SuperHouse/AQS/Images/AQSBCASE-v1_0-black-oblique.jpg

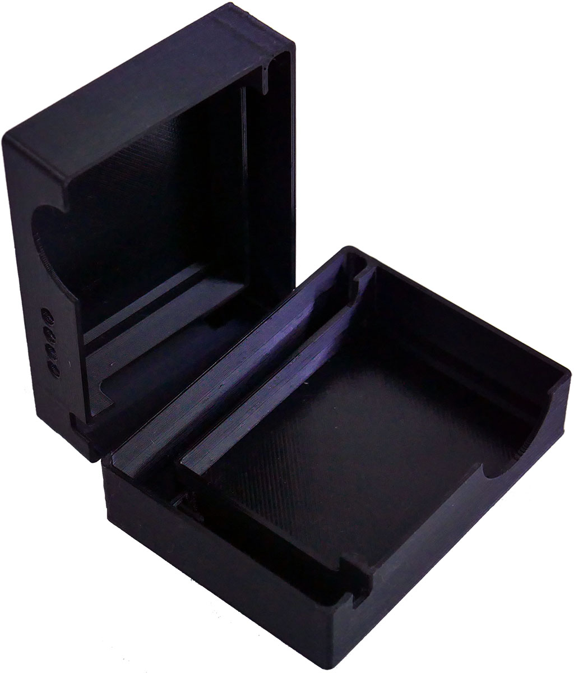
Images/AQSBCASE-v1_0-black-oblique.jpg
