SuperHouse/AQS/Images/AQSBCASE-v1_0-black-top.jpg

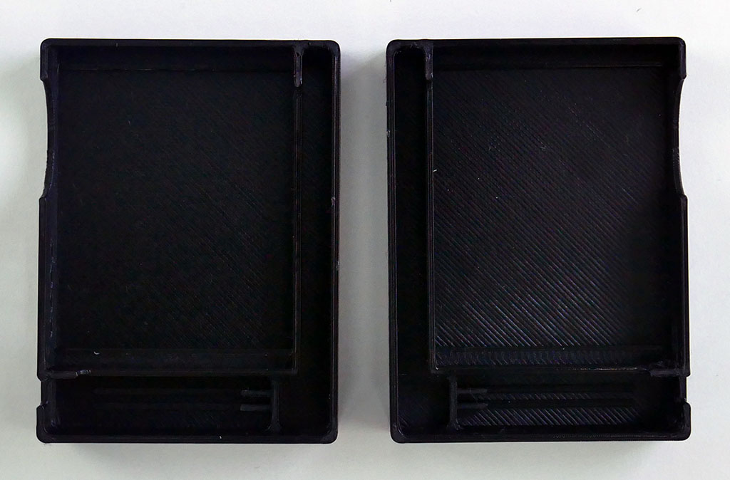
Images/AQSBCASE-v1_0-black-top.jpg
