SuperHouse/AQS/Images/AQSBCASE-v1_0-blue-top.jpg

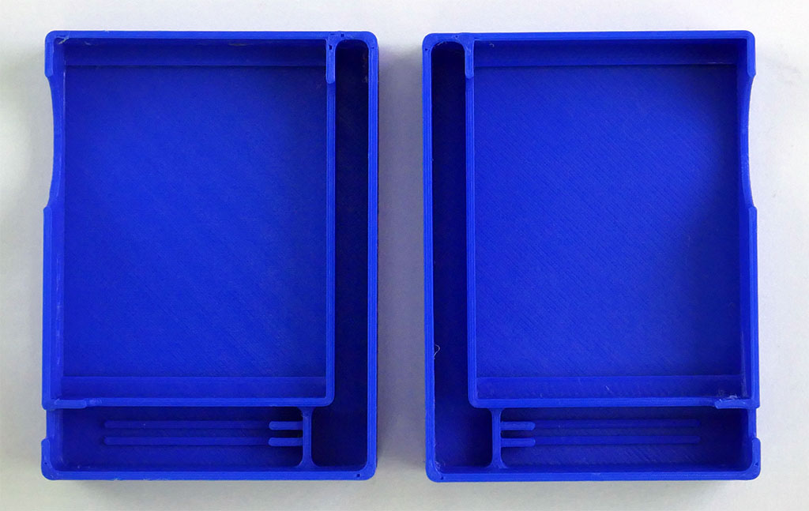
Images/AQSBCASE-v1_0-blue-top.jpg
