SuperHouse/AQS/Images/AQSBCASE-v1_0-green-oblique.jpg

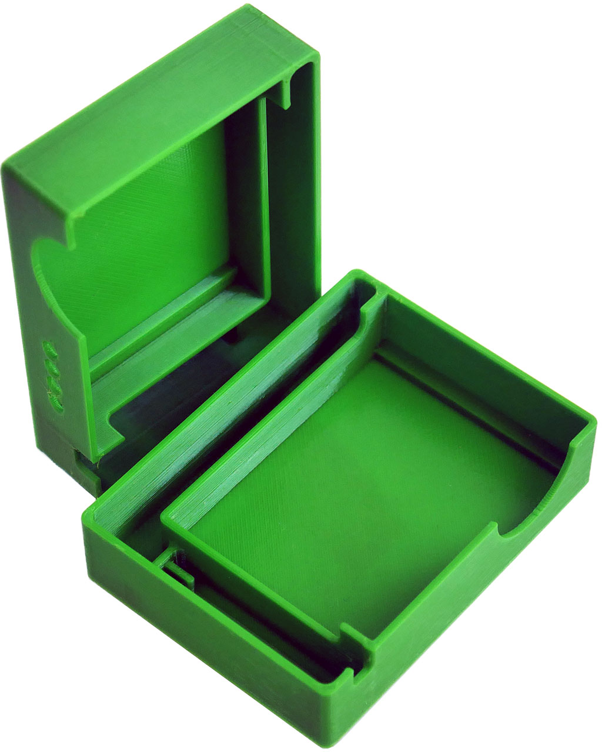
Images/AQSBCASE-v1_0-green-oblique.jpg
