SuperHouse/AQS/Images/AQSBCASE-v1_0-red-oblique.jpg

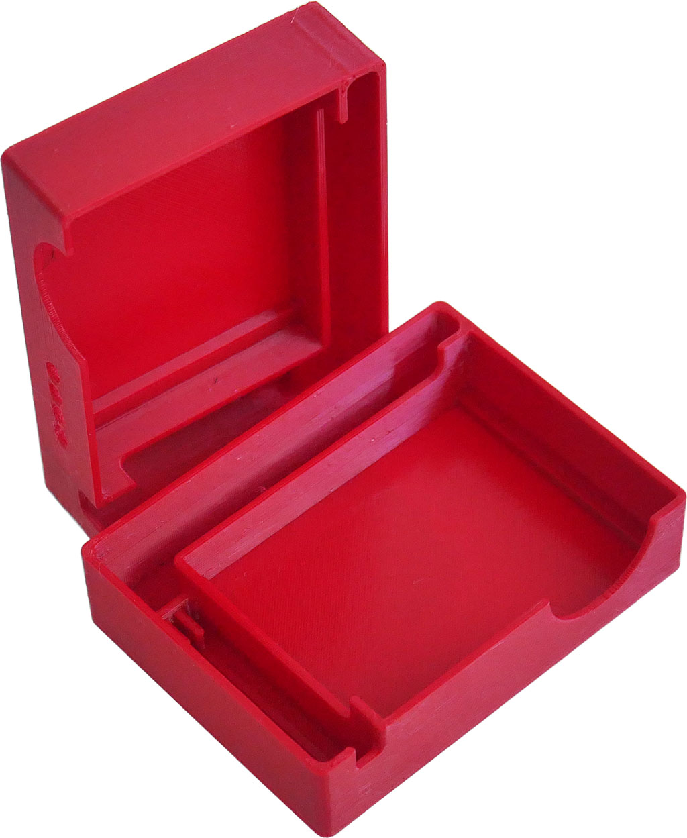
Images/AQSBCASE-v1_0-red-oblique.jpg
