SuperHouse/AQS/Images/AQSBCASE-v1_0-white-oblique.jpg

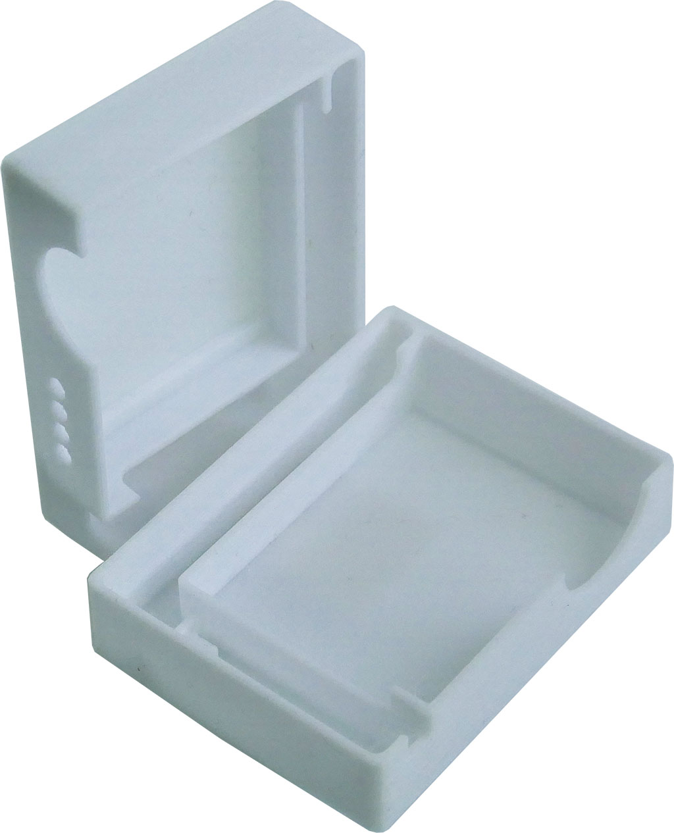
Images/AQSBCASE-v1_0-white-oblique.jpg
