SuperHouse/AQS/Images/AQSBCASE-v1_0-white-top.jpg

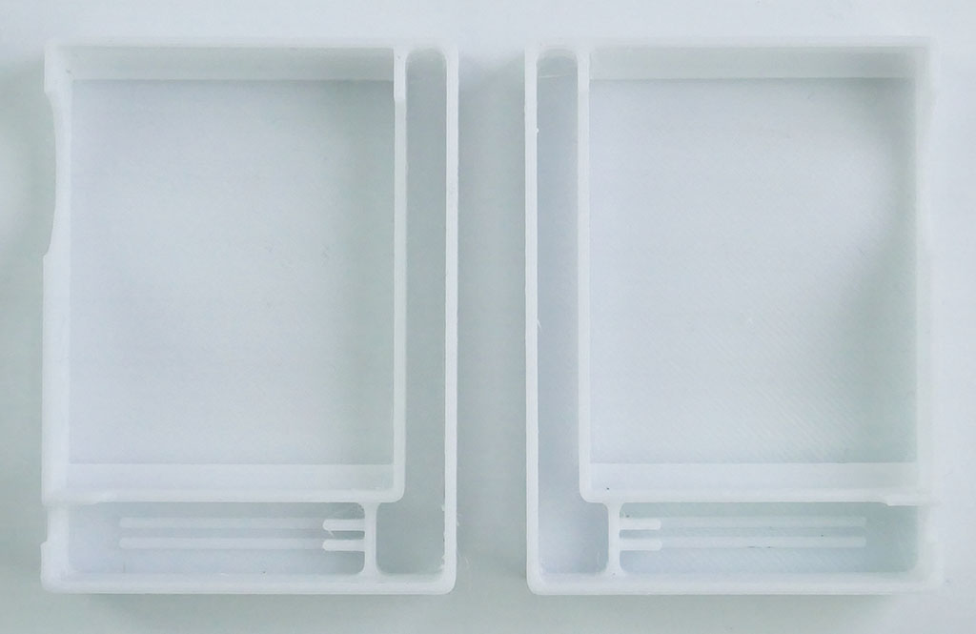
Images/AQSBCASE-v1_0-white-top.jpg
