SuperHouse/AQS/Images/AQSBCASE-v1_0-yellow-top.jpg

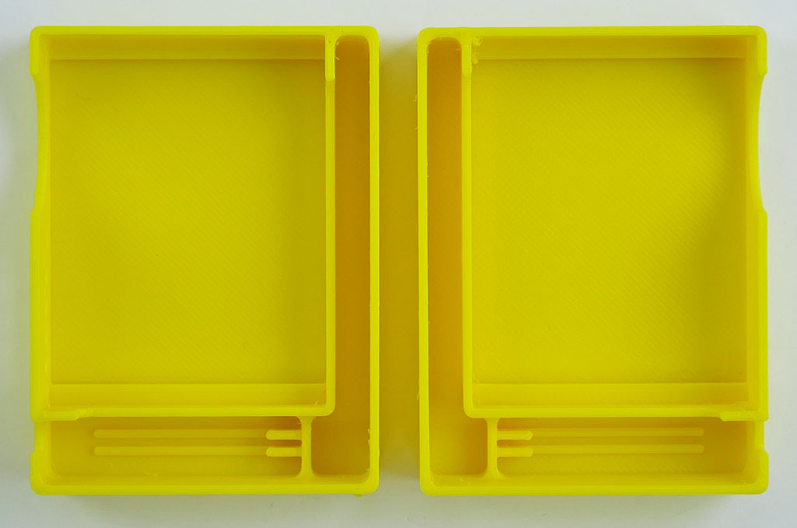
Images/AQSBCASE-v1_0-yellow-top.jpg
