SuperHouse/AQS/Images/AQSDCASE-v1_0-black-oblique.jpg

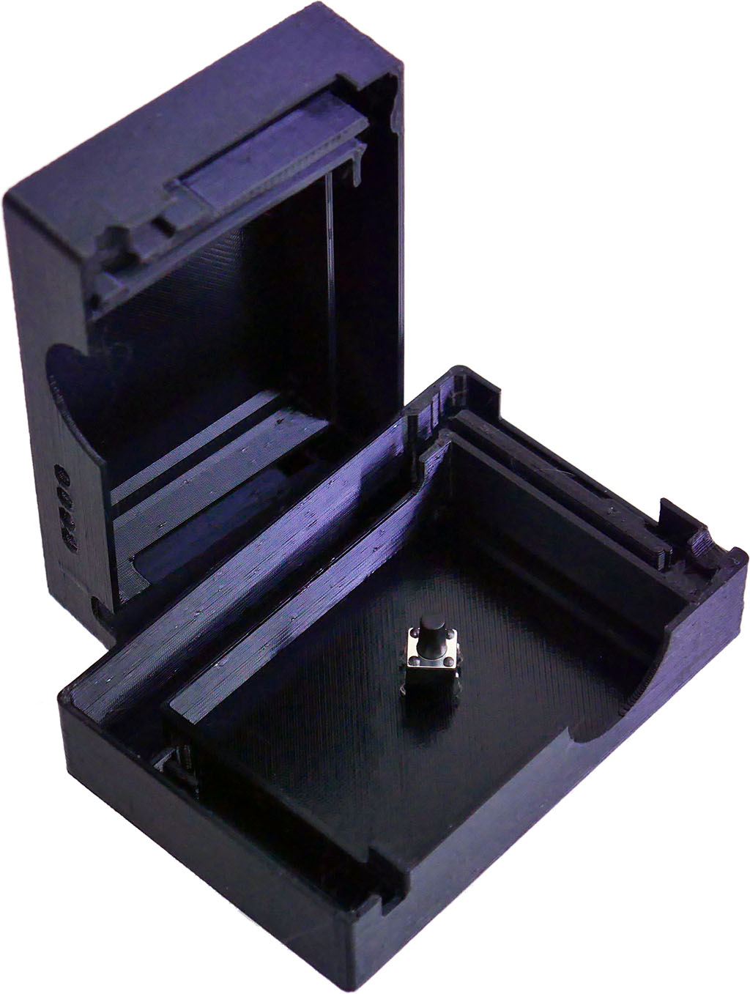
Images/AQSDCASE-v1_0-black-oblique.jpg
