SuperHouse/AQS/Images/AQSDCASE-v1_0-black-top.jpg

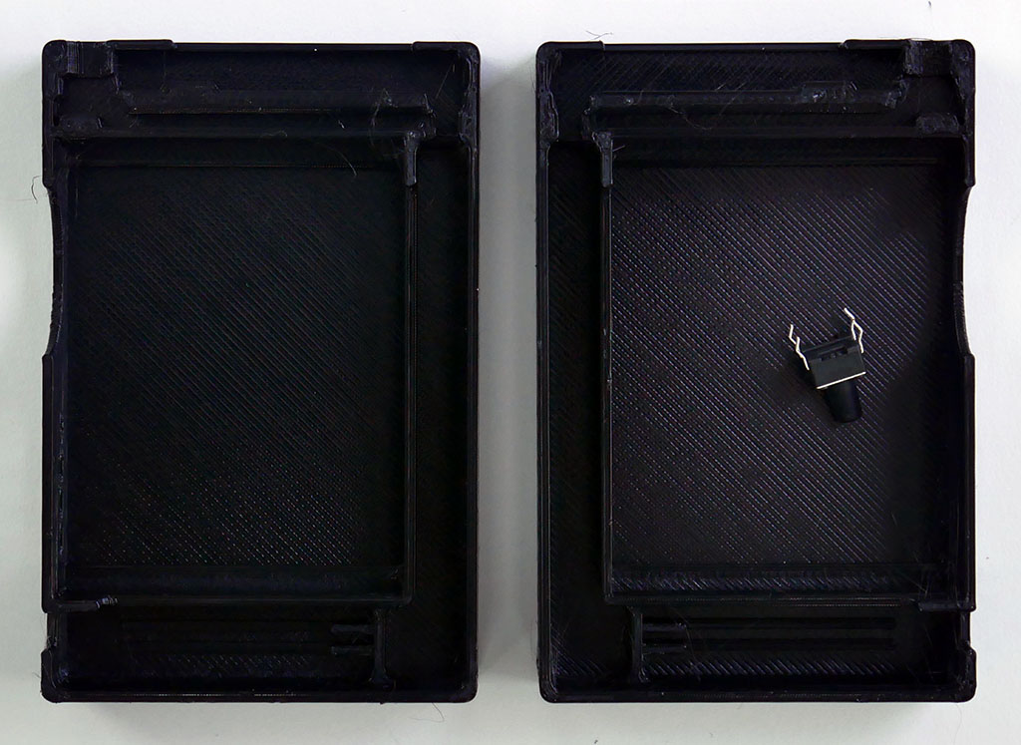
Images/AQSDCASE-v1_0-black-top.jpg
