SuperHouse/AQS/Images/AQSDCASE-v1_0-blue-oblique.jpg

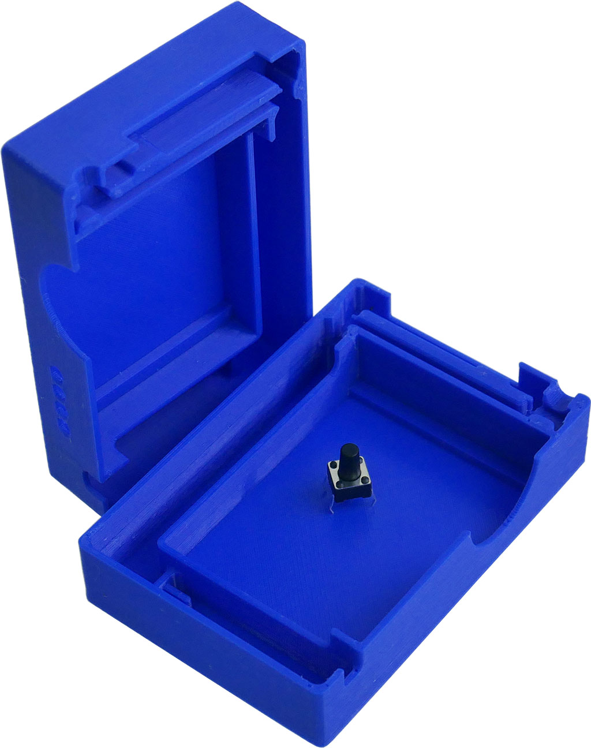
Images/AQSDCASE-v1_0-blue-oblique.jpg
