SuperHouse/AQS/Images/AQSDCASE-v1_0-blue-top.jpg

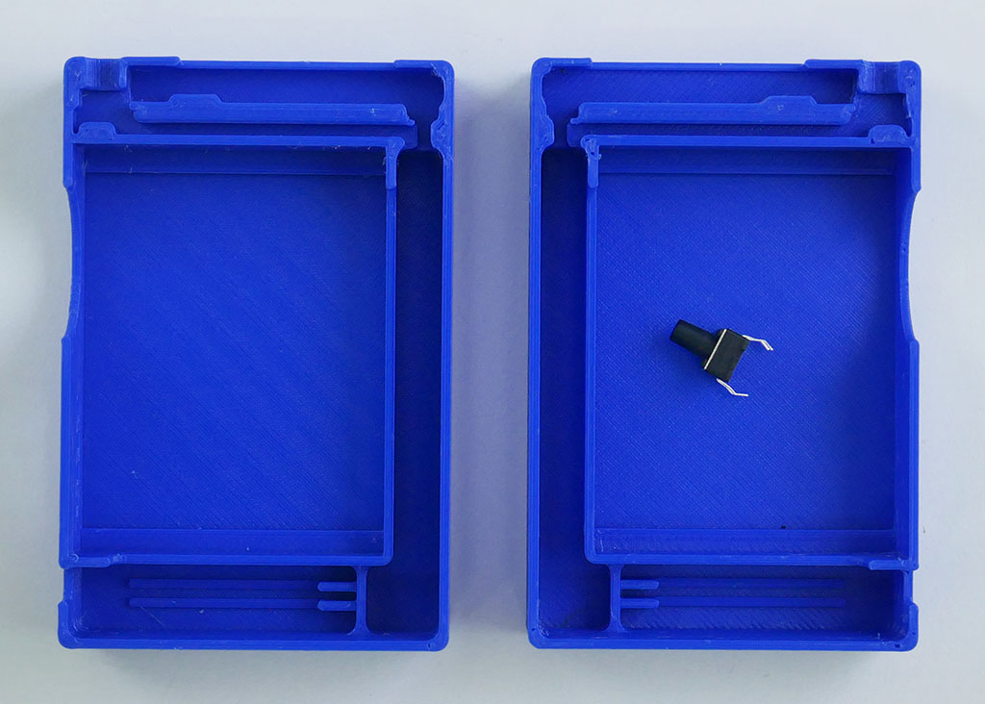
Images/AQSDCASE-v1_0-blue-top.jpg
