SuperHouse/AQS/Images/AQSDCASE-v1_0-translucent-oblique.jpg

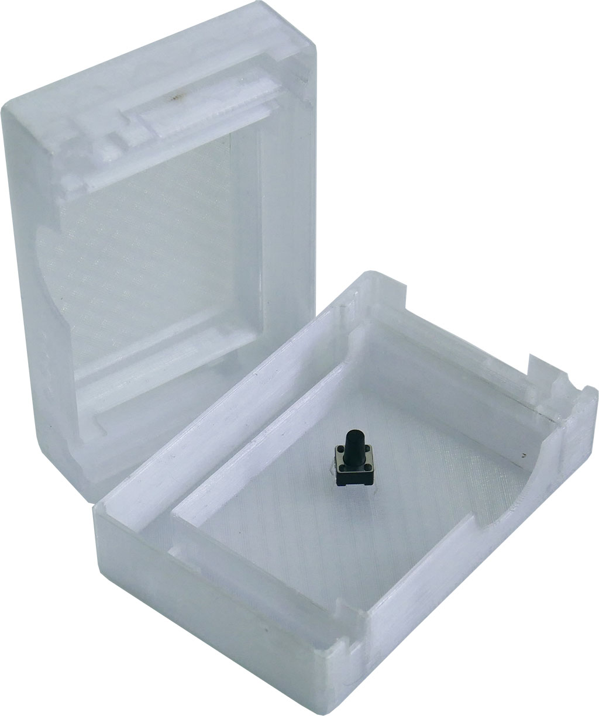
Images/AQSDCASE-v1_0-translucent-oblique.jpg
