SuperHouse/AQS/Images/AQSDCASE-v1_0-translucent-top.jpg

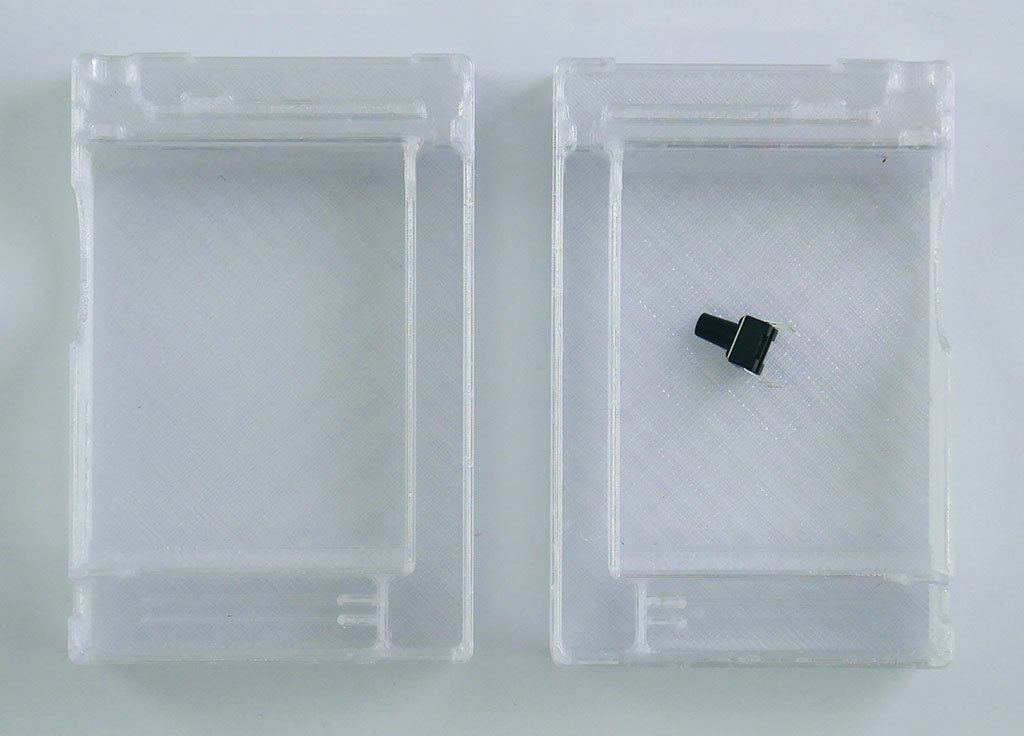
Images/AQSDCASE-v1_0-translucent-top.jpg
