SuperHouse/AQS/Images/AQSDCASE-v1_0-white-oblique.jpg

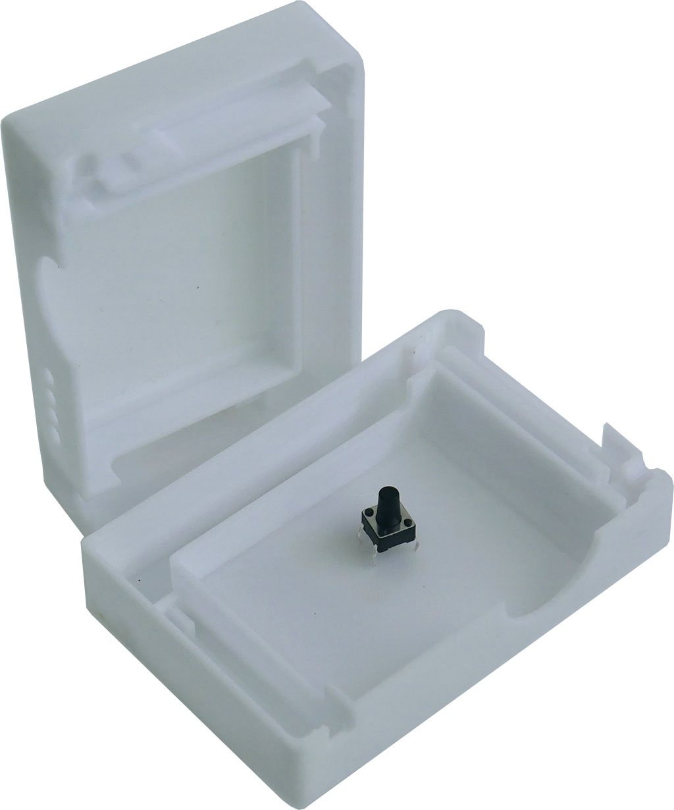
Images/AQSDCASE-v1_0-white-oblique.jpg
