SuperHouse/AQS/Images/AQSDCASE-v1_0-yellow-oblique.jpg

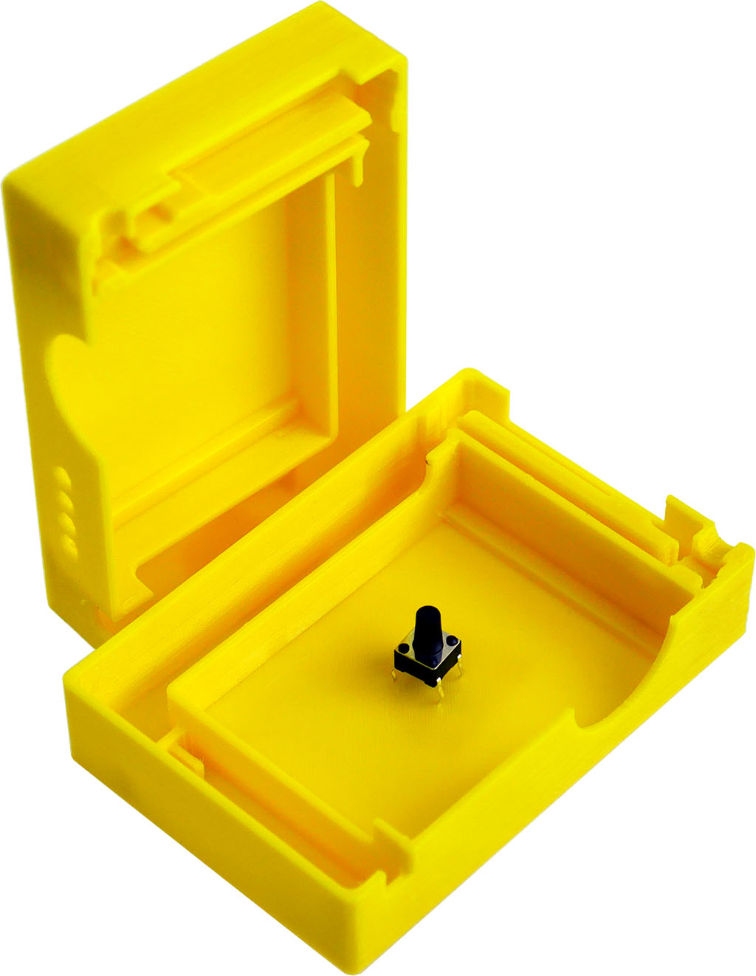
Images/AQSDCASE-v1_0-yellow-oblique.jpg
