SuperHouse/AQS/Images/AQSDCASE-v1_0-yellow-top.jpg

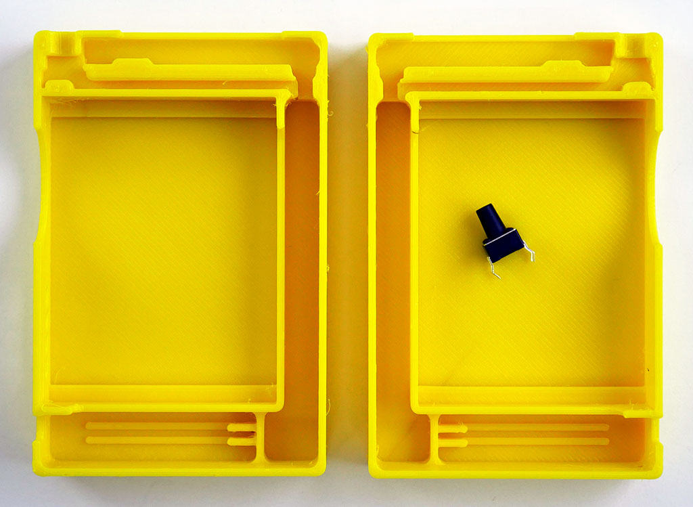
Images/AQSDCASE-v1_0-yellow-top.jpg
