SuperHouse/AQS/Images/P1030344.png

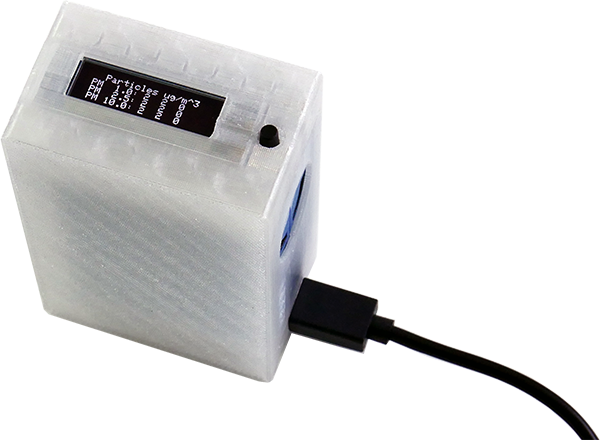
Images/P1030344.png
