SuperHouse/AQS/Images/P1030387.JPG

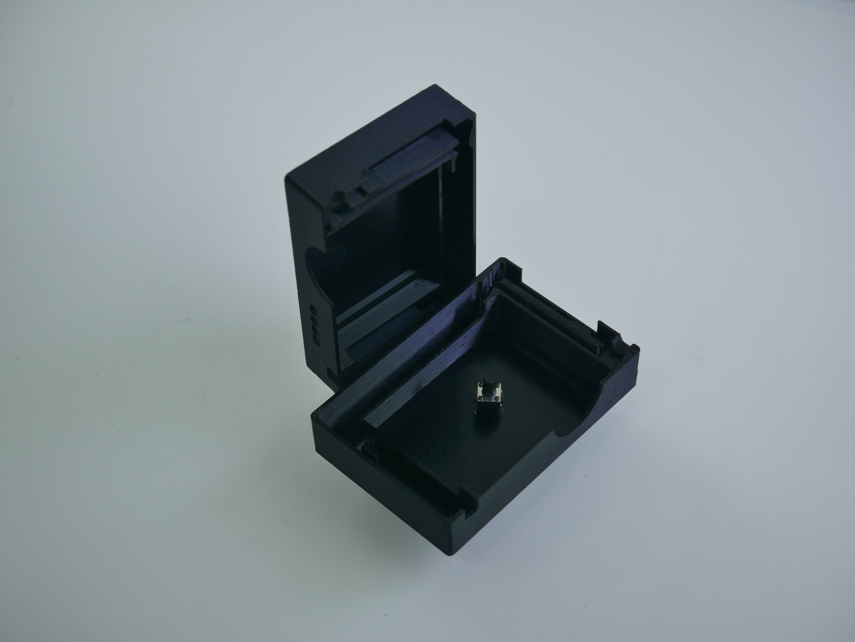
Images/P1030387.JPG
