SuperHouse/AQS/Images/Screen Shot 2020-12-06 at 8.37.48 pm.png

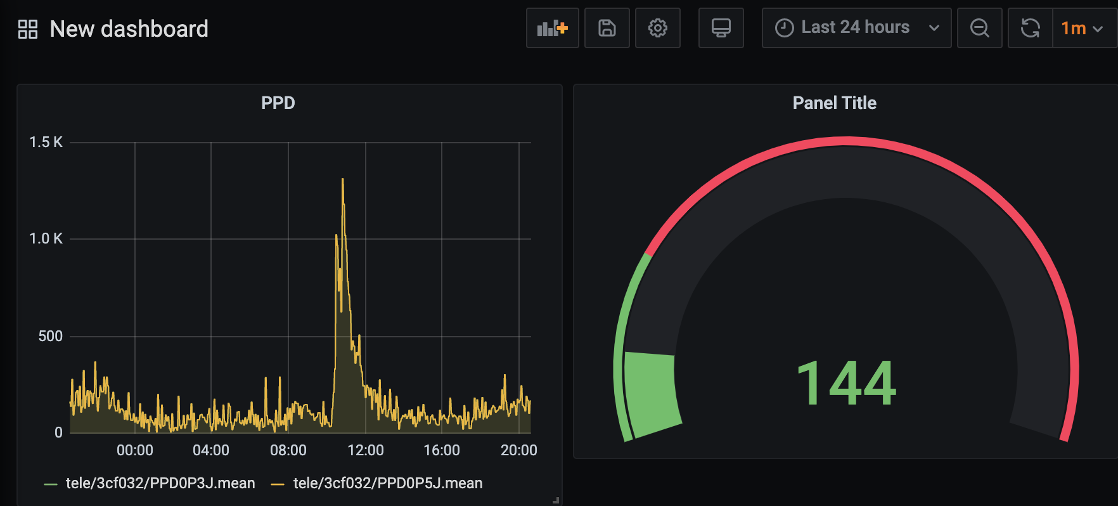
Images/Screen Shot 2020-12-06 at 8.37.48 pm.png
