SuperHouse/AQS/Images/tact-switch.jpg

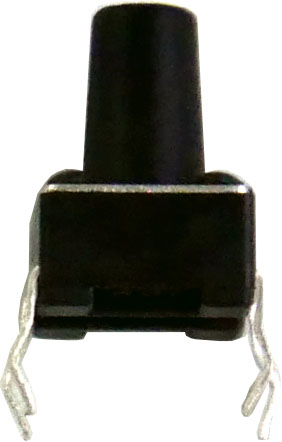
Images/tact-switch.jpg
