SuperHouse/AQS/Images/AQSB-assembly-2.jpg

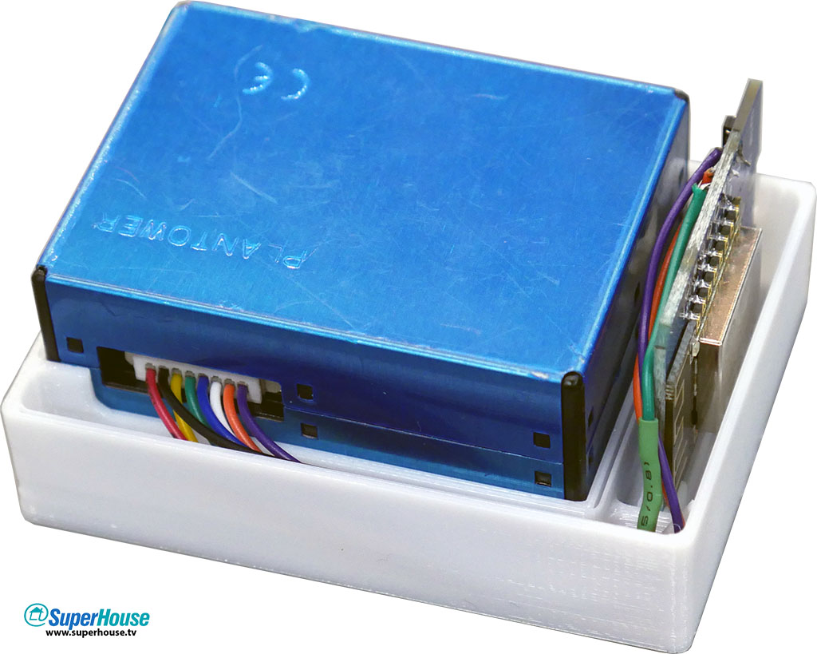
Images/AQSB-assembly-2.jpg
