SuperHouse/AQS/Images/AQSB-assembly-3.jpg

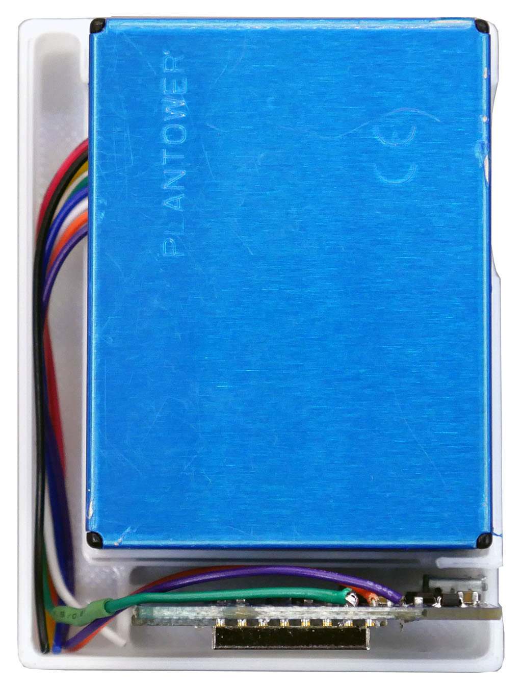
Images/AQSB-assembly-3.jpg
