SuperHouse/AQS/Images/AQSB-assembly.jpg

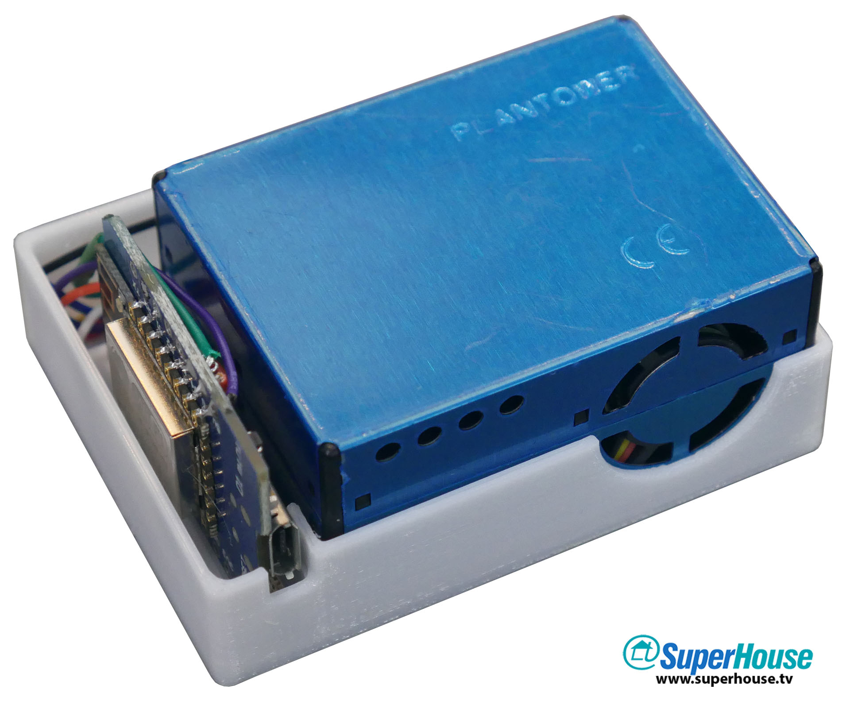
Images/AQSB-assembly.jpg
